natarii/MegaGRRL/firmware/main/options.c

#include "options.h"
#include "player.h"
#include "esp_log.h"
#include "driver.h"
#include "leddrv.h"
#include "loader.h"
#include "userled.h"
#include "ui/filebrowser.h"
#include "player.h"
#include "clk.h"
#include "pitch.h"
#include "ui.h"
#include <rom/crc.h>
#include "queue.h"
#include "sdcard.h"
#include "ui/modal.h"
#include "logmgr.h"

static const char* TAG = "OptionsMgr";

static volatile bool OptionsMgr_Unsaved = false;
static volatile uint8_t OptionsMgr_ShittyTimer = 0;

const char *OptionCatNames[OPTION_CATEGORY_COUNT] = {
    "General",
    "File Browser",
    "LEDs",
    "Playback",
    "Advanced",
    "Beta Features",
    //"Screen", portable only, so getting rid of it for now
};

static void opts_mutingupdate() {
    xEventGroupSetBits(Driver_CommandEvents, DRIVER_EVENT_UPDATE_MUTING);
}

static void opts_pitchupdate() {
    Pitch_Adjust(Pitch_Get()); //this will snap down to the max locked clock if they switch from unlocked -> locked
}

static void wrap_leddrv_updatebrightness() {
    LedDrv_UpdateBrightness(false);
}

static bool loaded[OPTION_COUNT];

//last used: 0018
const option_t Options[OPTION_COUNT] = {
    {
        0x0001,
        "Play mode",
        "Playlist behavior",
        OPTION_CATEGORY_PLAYBACK,
        OPTION_TYPE_NUMERIC,
        OPTION_SUBTYPE_PLAYMODE,
        &Player_RepeatMode,
        REPEAT_ALL,
        NULL,
        NULL
    },
    {
        0x0000,
        "Loop count",
        "Number of times the looping section of the track should be played",
        OPTION_CATEGORY_PLAYBACK,
        OPTION_TYPE_NUMERIC,
        OPTION_SUBTYPE_LOOPS,
        &Player_LoopCount,
        2,
        NULL,
        NULL
    },/*
    {
        "vgm_trim mitigation",
        "Silence erroneous notes at start of track caused by vgm_trim.",
        OPTION_CATEGORY_PLAYBACK,
        OPTION_TYPE_BOOL,
        &Driver_MitigateVgmTrim,
        true,
        NULL
    },*//*
    {
        "Allow PCM across block boundaries",
        "Allow PCM to be played across data block boundaries. No VGMs are known to require this, so it is recommended to leave this off. Enabling this may cause significant slowdown.",
        OPTION_CATEGORY_PLAYBACK,
        OPTION_TYPE_BOOL,
        NULL, //
        false,
        NULL
    },
    {
        "Correct DCSG frequency",
        "Automatically correct for differences between discrete TI DCSGs and Sega VDP DCSGs when channel frequency is set to 0.",
        OPTION_CATEGORY_PLAYBACK,
        OPTION_TYPE_BOOL,
        &Driver_FixDcsgFrequency,
        true,
        NULL
    },*/
    {
        0x0012,
        "Shuffle",
        "Randomize order of playback",
        OPTION_CATEGORY_PLAYBACK,
        OPTION_TYPE_BOOL,
        OPTION_SUBTYPE_SHUFFLE,
        &Queue_Shuffle,
        false,
        NULL,
        NULL
    },
    {
        0x0003,
        "Stereo/Mono toggle",
        "Setting this to mono will force mono sound in all VGMs.",
        OPTION_CATEGORY_PLAYBACK,
        OPTION_TYPE_BOOL,
        OPTION_SUBTYPE_STEREOMONO,
        &Driver_ForceMono,
        false,
        opts_mutingupdate,
        opts_mutingupdate
    },
    {
        0x0015,
        "LED brightness",
        "Overall LED brightness",
        OPTION_CATEGORY_LEDS,
        OPTION_TYPE_NUMERIC,
        OPTION_SUBTYPE_BRIGHTNESS,
        &LedDrv_Brightness,
        5,
        wrap_leddrv_updatebrightness,
        wrap_leddrv_updatebrightness
    },
    {
        0x000e,
        "Fade out at end",
        "Enables and disables fading out at the end of each track.",
        OPTION_CATEGORY_PLAYBACK,
        OPTION_TYPE_BOOL,
        OPTION_SUBTYPE_NONE,
        &Driver_FadeEnabled,
        true,
        NULL,
        NULL
    },
    {
        0x000f,
        "Fade length",
        "Length of fade out, in seconds",
        OPTION_CATEGORY_PLAYBACK,
        OPTION_TYPE_NUMERIC,
        OPTION_SUBTYPE_FADELENGTH,
        &Driver_FadeLength,
        3,
        NULL,
        NULL
    },
    {
        0x0002,
        "Ignore zero-sample loops",
        "Some badly made VGMs specify a loop offset without a loop length. Deflemask is known to do this. Turning this option off will fix looping in some broken VGMs, but will cause unwanted looping in other broken VGMs.",
        OPTION_CATEGORY_PLAYBACK,
        OPTION_TYPE_BOOL,
        OPTION_SUBTYPE_NONE,
        &Loader_IgnoreZeroSampleLoops,
        true,
        NULL,
        NULL
    },
    {
        0x0016,
        "Skip unsupported VGMs",
        "Skip VGMs that cannot be played on the hardware.",
        OPTION_CATEGORY_PLAYBACK,
        OPTION_TYPE_BOOL,
        OPTION_SUBTYPE_NONE,
        &Player_SkipUnsupported,
        true,
        NULL,
        NULL
    },
    {
        0x0017,
        "Assume SEGA DCSG",
        "Improve support for SEGA console VGM files by assuming the SN76489 is the SEGA type. This should only be disabled when playing VGMs from systems using discrete SN76489 chips.",
        OPTION_CATEGORY_PLAYBACK,
        OPTION_TYPE_BOOL,
        OPTION_SUBTYPE_NONE,
        &Driver_AssumeSegaDcsg,
        true,
        NULL,
        NULL
    },
    {
        0x0005,
        "User LED A source",
        "Sets the source of User LED A.",
        OPTION_CATEGORY_LEDS,
        OPTION_TYPE_NUMERIC,
        OPTION_SUBTYPE_USERLED,
        &UserLedMgr_Source[0],
        USERLED_SRC_PLAYPAUSE,
        NULL,
        NULL
    },
    {
        0x0006,
        "User LED B source",
        "Sets the source of User LED B.",
        OPTION_CATEGORY_LEDS,
        OPTION_TYPE_NUMERIC,
        OPTION_SUBTYPE_USERLED,
        &UserLedMgr_Source[1],
        USERLED_SRC_DISK_ALL,
        NULL,
        NULL
    },
    {
        0x0007,
        "User LED C source",
        "Sets the source of User LED C.",
        OPTION_CATEGORY_LEDS,
        OPTION_TYPE_NUMERIC,
        OPTION_SUBTYPE_USERLED,
        &UserLedMgr_Source[2],
        USERLED_SRC_NONE,
        NULL,
        NULL
    },
    {
        0x0008,
        "Sort directory contents",
        "Enabling this sorts directory contents according to the sorting options. When disabled, contents will be displayed in the order they are found in the filesystem.",
        OPTION_CATEGORY_FILEBROWSER,
        OPTION_TYPE_BOOL,
        OPTION_SUBTYPE_NONE,
        &Ui_FileBrowser_Sort,
        true,
        Ui_FileBrowser_InvalidateDirEntry,
        NULL
    },
    {
        0x0009,
        "Alphabetical sort direction",
        "Sets whether directory contents are sorted in ascending or descending order.",
        OPTION_CATEGORY_FILEBROWSER,
        OPTION_TYPE_NUMERIC,
        OPTION_SUBTYPE_SORTDIR,
        &Ui_FileBrowser_SortDir,
        SORT_ASCENDING,
        Ui_FileBrowser_InvalidateDirEntry,
        NULL
    },
    {
        0x000a,
        "Sort dirs before files",
        "Sets whether directories appear before files.",
        OPTION_CATEGORY_FILEBROWSER,
        OPTION_TYPE_BOOL,
        OPTION_SUBTYPE_NONE,
        &Ui_FileBrowser_DirsBeforeFiles,
        true,
        Ui_FileBrowser_InvalidateDirEntry,
        NULL
    },
    {
        0x0011,
        "Text scroll type",
        "Method by which long text will be scrolled",
        OPTION_CATEGORY_GENERAL,
        OPTION_TYPE_NUMERIC,
        OPTION_SUBTYPE_SCROLLTYPE,
        &Ui_ScrollType,
        SCROLLTYPE_PINGPONG,
        NULL, //note: if there are ever any global ui elements this applies to, we need to set a callback to force changes on them
        NULL
    },
    {
        0x000b,
        "Overwrite VGZ files",
        "When this is enabled, VGZ files will be overwritten with extracted VGM equivalents when first played. This will replace the files on the SD card, but will result in much shorter track load times on future plays.",
        OPTION_CATEGORY_GENERAL,
        OPTION_TYPE_BOOL,
        OPTION_SUBTYPE_NONE,
        &Player_UnvgzReplaceOriginal,
        true,
        NULL,
        NULL
    },
    {
        0x000c,
        "Narrow font",
        "Use a narrow font in the file browser.",
        OPTION_CATEGORY_FILEBROWSER,
        OPTION_TYPE_BOOL,
        OPTION_SUBTYPE_NONE,
        &Ui_FileBrowser_Narrow,
        false,
        NULL,
        NULL
    },
    {
        0x000d,
        "Unlock pitch",
        "Allow additional pitch adjustment. Warning: Sound chips will be overclocked.",
        OPTION_CATEGORY_ADVANCED,
        OPTION_TYPE_BOOL,
        OPTION_SUBTYPE_NONE,
        &Clk_Unlock,
        false,
        opts_pitchupdate,
        NULL
    },
    {
        0x0010,
        "Fast OPNA ADPCM upload",
        "Increases OPNA ADPCM upload speed. Warning: Sound chip will be overclocked.",
        OPTION_CATEGORY_ADVANCED,
        OPTION_TYPE_BOOL,
        OPTION_SUBTYPE_NONE,
        &Loader_FastOpnaUpload,
        false,
        NULL,
        NULL
    },
    {
        0x0014,
        "Log level",
        "Change the serial port log level. Values other than Normal will cause slight performance decrease.",
        OPTION_CATEGORY_ADVANCED,
        OPTION_TYPE_NUMERIC,
        OPTION_SUBTYPE_LOGLEVEL,
        &logmgr_loglevel,
        0,
        logmgr_update_loglevel,
        NULL
    },
    {
        0x0018,
        "Enable fast-forwarding",
        "Enables beta support for fast-forwarding through VGMs.",
        OPTION_CATEGORY_BETA,
        OPTION_TYPE_BOOL,
        OPTION_SUBTYPE_NONE,
        &Player_EnableFastForward,
        false,
        NULL,
        NULL
    },
};

static void file_error() {
    modal_show_simple(TAG, "SD Card Error", "There was an error saving settings to the SD card.\nPlease check that the card is inserted and has free space.", LV_SYMBOL_OK " OK");
    Sdcard_Invalidate();
    Ui_Screen = UISCREEN_MAINMENU;
}

void OptionsMgr_Save() {
    ESP_LOGW(TAG, "saving options");
    FILE *f = fopen("/sd/.mega/options.mgo", "w");
    if (!f) {
        OptionsMgr_Unsaved = true;
        file_error();
        ESP_LOGE(TAG, "IO error opening options file for write...");
        return;
    }
    uint32_t tmp = OPTIONS_VER;
    fwrite(&tmp, 1, 1, f);
    uint32_t crc = 0;
    fwrite(&crc, 4, 1, f); //alloc space for crc
    tmp = OPTION_COUNT;
    fwrite(&tmp, 1, 1, f);
    crc = crc32_le(crc, (uint8_t*)&tmp, 1);
    for (uint8_t i=0;i<OPTION_COUNT;i++) {
        fwrite(&Options[i].uid, 2, 1, f);
        crc = crc32_le(crc, (uint8_t*)&Options[i].uid, 2);
        if (Options[i].var == NULL) {
            tmp = 0;
            fwrite(&tmp, 1, 1, f);
            crc = crc32_le(crc, (uint8_t*)&tmp, 1);
            continue;
        }
        fwrite((uint8_t*)Options[i].var, 1, 1, f);
        crc = crc32_le(crc, (uint8_t*)Options[i].var, 1);
    }
    //now write out the crc
    fseek(f, 1, SEEK_SET);
    fwrite(&crc, 4, 1, f);
    if (ferror(f)) {
        OptionsMgr_Unsaved = true;
        file_error();
        ESP_LOGE(TAG, "IO error writing options file...");
        fclose(f);
        return;
    }
    fclose(f);
    ESP_LOGW(TAG, "options saved");
}

static uint8_t loadoptionsfile(const char *filename) {
    ESP_LOGI(TAG, "checking options file %s", filename);
    FILE *f = fopen(filename, "r");
    if (f == NULL) {
        ESP_LOGI(TAG, "no options file exists");
        return 1;
    }
    uint32_t tmp = 0;
    fread(&tmp, 1, 1, f);
    //note: we still support version A0 files, it was the ver prior to the CRC being added
    if (tmp != OPTIONS_VER && tmp != 0xa0) {
        ESP_LOGW(TAG, "options file bad ver 0x%02x", tmp);
        fclose(f);
        return 2;
    }
    ESP_LOGI(TAG, "file ver 0x%02x", tmp);
    if (tmp != 0xa0) { //we have a crc
        ESP_LOGI(TAG, "Verifying crc");
        fread(&tmp, 4, 1, f); //file's crc
        uint32_t curpos = ftell(f);
        fseek(f, 0, SEEK_END);
        uint32_t remaining = ftell(f) - curpos;
        //nobody else is using pcmbuf right now, so we can stash some stuff there
        fseek(f, curpos, SEEK_SET);
        fread(Driver_PcmBuf, 1, remaining, f);
        uint32_t crc = 0;
        crc = crc32_le(crc, Driver_PcmBuf, remaining);
        if (tmp != crc) {
            ESP_LOGE(TAG, "options file bad crc!!!");
            fclose(f);
            return 3;
        }
        fseek(f, curpos, SEEK_SET); //back to where we were
        ESP_LOGI(TAG, "crc all good");
        tmp = 0;
    } else {
        ESP_LOGI(TAG, "Old version, no crc to verify");
    }
    fread(&tmp, 1, 1, f);
    ESP_LOGI(TAG, "file contains %d options", tmp);
    for (uint8_t i=0;i<tmp;i++) {
        uint16_t uid = 0;
        fread(&uid, 2, 1, f);
        uint8_t v = 0;
        fread(&v, 1, 1, f);
        bool found = false;
        for (uint8_t j=0;j<OPTION_COUNT;j++) {
            if (Options[j].uid == uid) {
                found = true;
                if (uid == 0x0011 && v == 2) { //"truncate" scroll type got deleted
                    ESP_LOGW(TAG, "Fixing unsupported scroll type");
                    v = SCROLLTYPE_PINGPONG;
                    OptionsMgr_Touch();
                }
                if (Options[j].var != NULL) *(volatile uint8_t*)Options[j].var = v;
                if (Options[j].cb_initial != NULL) Options[j].cb_initial();
                loaded[j] = true;
                ESP_LOGI(TAG, "applied option uid %d - %d", uid, v);
                break;
            }
        }
        if (!found) {
            if (uid == 0x0004) { //old led brightness, new is 0015
                //find the nearest new brightness setting to the old one
                uint8_t newval = 0;
                for (uint8_t j=0;j<sizeof(global_bright_lut);j++) {
                    if (global_bright_lut[j] > v) break;
                    newval = j;
                }
                ESP_LOGW(TAG, "Remapping old LED brightness %d to new value %d (%d)", v, newval, global_bright_lut[newval]);
                for (uint8_t j=0;j<OPTION_COUNT;j++) {
                    if (Options[j].uid == 0x0015) {
                        if (Options[j].var != NULL) *(volatile uint8_t*)Options[j].var = newval;
                        if (Options[j].cb_initial != NULL) Options[j].cb_initial();
                        loaded[j] = true;
                        break;
                    }
                }
                OptionsMgr_Touch();
            } else {
                ESP_LOGW(TAG, "skipping unknown option uid %d", uid);
            }
        }
    }
    fclose(f);
    ESP_LOGI(TAG, "finished loading options file");
    return 0;
}

void OptionsMgr_Setup() {
    //load options, apply defaults if file not found, if file is corrupt try a backup
    memset(&loaded, false, OPTION_COUNT);

    uint8_t ret = loadoptionsfile("/sd/.mega/options.mgo");
    if (ret == 3) { //corrupt, try the backup
        ret = loadoptionsfile("/sd/.mega/options.bak");
        //return value doesn't really matter now, if it's bad version/corrupt/doesn't exist it just won't apply anything, and we'll set defaults below
    } else if (ret == 0) { //loaded alright, let's take a backup
        ESP_LOGI(TAG, "Backing up options file...");
        FILE *o = fopen("/sd/.mega/options.mgo", "r");
        FILE *b = fopen("/sd/.mega/options.bak", "w");
        fseek(o, 0, SEEK_END);
        uint32_t s = ftell(o);
        fseek(o, 0, SEEK_SET);
        fread(Driver_PcmBuf, 1, s, o);
        fwrite(Driver_PcmBuf, 1, s, b);
        fclose(b);
        fclose(o);
        ESP_LOGI(TAG, "Backup done");
    }

    for (uint8_t i=0;i<OPTION_COUNT;i++) {
        if (!loaded[i]) {
            if (Options[i].var != NULL) *(volatile uint8_t*)Options[i].var = (uint8_t)Options[i].defaultval;
            if (Options[i].cb_initial != NULL) Options[i].cb_initial();
            ESP_LOGW(TAG, "applied defaults for option uid %d", Options[i].uid);
        }
    }

    ESP_LOGI(TAG, "done");
}

void OptionsMgr_Touch() {
    OptionsMgr_Unsaved = true;
    OptionsMgr_ShittyTimer = 0;
}

void OptionsMgr_Main() {
    while (1) {
        if (OptionsMgr_Unsaved && OptionsMgr_ShittyTimer++ == 2) {
            OptionsMgr_ShittyTimer = 0;
            if (Sdcard_IsOnline()) {
                OptionsMgr_Unsaved = false;
                OptionsMgr_Save();
            } else {
                ESP_LOGW(TAG, "Skipping saving, SD card is offline");
            }
        }
        vTaskDelay(pdMS_TO_TICKS(1000));
    }
}
