natarii/MegaGRRL/firmware/main/img.c

#include "lvgl.h"
#include "hal.h"

#ifndef LV_ATTRIBUTE_MEM_ALIGN
#define LV_ATTRIBUTE_MEM_ALIGN
#endif

#ifdef HWVER_PORTABLE
const LV_ATTRIBUTE_MEM_ALIGN uint8_t img_frame_map[] = {
  0xff, 0xff, 0xff, 0xff, 	/*Color of index 0*/
  0x00, 0x00, 0x00, 0xff, 	/*Color of index 1*/

  0x00, 0x00, 0x00, 0x00, 0x00, 0x00, 0x00, 
  0x00, 0x00, 0x00, 0x00, 0x00, 0x00, 0x00, 
  0x3f, 0xff, 0xff, 0xff, 0xff, 0xff, 0x00, 
  0x3f, 0xff, 0xff, 0xff, 0xff, 0xff, 0x00, 
  0x3f, 0xff, 0xff, 0xff, 0xff, 0xff, 0x00, 
  0x3f, 0xff, 0xff, 0xff, 0xff, 0xff, 0x00, 
  0x3f, 0xff, 0xff, 0xff, 0xff, 0xff, 0x00, 
  0x3f, 0xff, 0xf0, 0x00, 0x00, 0x01, 0x00, 
  0x3f, 0xff, 0xf7, 0xff, 0xff, 0xfd, 0x00, 
  0x39, 0x9f, 0xf7, 0xff, 0xff, 0xfd, 0x00, 
  0x39, 0x9f, 0xf7, 0xff, 0xff, 0xfd, 0x00, 
  0x3f, 0xff, 0xf7, 0xff, 0xff, 0xfd, 0x00, 
  0x3f, 0xff, 0xf7, 0xff, 0xff, 0xfd, 0x00, 
  0x39, 0x9f, 0xf7, 0xff, 0xff, 0xfd, 0x00, 
  0x39, 0x9f, 0xf7, 0xff, 0xff, 0xfd, 0x00, 
  0x3f, 0xff, 0xf7, 0xff, 0xff, 0xfd, 0x00, 
  0x3f, 0xff, 0xf7, 0xff, 0xff, 0xfd, 0x00, 
  0x39, 0x9f, 0xf7, 0xff, 0xff, 0xfd, 0x00, 
  0x39, 0x9f, 0xf7, 0xff, 0xff, 0xfd, 0x00, 
  0x3f, 0xff, 0xf7, 0xff, 0xff, 0xfd, 0x00, 
  0x3f, 0xff, 0xf7, 0xff, 0xff, 0xfd, 0x00, 
  0x39, 0xff, 0xf7, 0xff, 0xff, 0xfd, 0x00, 
  0x39, 0xff, 0xf7, 0xff, 0xff, 0xfd, 0x00, 
  0x3f, 0xff, 0xf7, 0xff, 0xff, 0xfd, 0x00, 
  0x3f, 0xff, 0xf7, 0xff, 0xff, 0xfd, 0x00, 
  0x39, 0xff, 0xf7, 0xff, 0xff, 0xfd, 0x00, 
  0x39, 0xff, 0xf7, 0xff, 0xff, 0xfd, 0x00, 
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
};

const lv_img_dsc_t img_kunoichilabs_smol = {
  .header.always_zero = 0,
  .header.w = 157,
  .header.h = 18,
  .data_size = 1486,
  .header.cf = LV_IMG_CF_INDEXED_4BIT,
  .data = img_kunoichilabs_smol_map,
};
