natarii/MegaGRRL/firmware/main/vgm.c

#include "vgm.h"
#include "esp_log.h"
#include "math.h"

static const char* TAG = "Vgm";

static const uint8_t CommandLengthLUT[256] = {
    /*  0  1  2  3  4  5  6  7  8  9  a  b  c  d  e  f*/
        0, 0, 0, 0, 0, 0, 0, 0, 0, 0, 0, 0, 0, 0, 0, 0, //0x00
        0, 0, 0, 0, 0, 0, 0, 0, 0, 0, 0, 0, 0, 0, 0, 0, //0x10
        0, 0, 0, 0, 0, 0, 0, 0, 0, 0, 0, 0, 0, 0, 0, 0, //0x20
        2, 2, 0, 0, 0, 0, 0, 0, 0, 0, 0, 0, 0, 0, 0, 2, //0x30
        0, 0, 0, 0, 0, 0, 0, 0, 0, 0, 0, 0, 0, 0, 0, 2, //0x40
        2, 3, 3, 3, 3, 3, 3, 3, 3, 3, 3, 3, 3, 3, 3, 3, //0x50
        0, 3, 1, 1, 0, 0, 1, 0, 0, 0, 0, 0, 0, 0, 0, 0, //0x60
        1, 1, 1, 1, 1, 1, 1, 1, 1, 1, 1, 1, 1, 1, 1, 1, //0x70
        1, 1, 1, 1, 1, 1, 1, 1, 1, 1, 1, 1, 1, 1, 1, 1, //0x80
        5, 5, 6,11, 2, 5, 0, 0, 0, 0, 0, 0, 0, 0, 0, 0, //0x90
        3, 3, 3, 3, 3, 3, 3, 3, 3, 3, 3, 3, 3, 3, 3, 3, //0xa0
        3, 3, 3, 3, 3, 3, 3, 3, 3, 3, 3, 3, 3, 3, 3, 3, //0xb0
        4, 4, 4, 4, 4, 4, 4, 4, 4, 4, 4, 4, 4, 4, 4, 4, //0xc0
        4, 4, 4, 4, 4, 4, 4, 0, 0, 0, 0, 0, 0, 0, 0, 0, //0xd0
        5, 5, 0, 0, 0, 0, 0, 0, 0, 0, 0, 0, 0, 0, 0, 0, //0xe0
        0, 0, 0, 0, 0, 0, 0, 0, 0, 0, 0, 0, 0, 0, 0, 2, //0xf0
};

uint8_t VgmCommandLength(uint8_t Command) { //including the command itself. only for fixed size commands
    uint8_t val = CommandLengthLUT[Command];
    if (val) return val;
    ESP_LOGW(TAG, "Vgm_CommandLength got bad command 0x%02x !!", Command);
    return 0xff;
}

bool VgmCommandIsFixedSize(uint8_t Command) {
    if (Command == 0x67 || Command == 0x68) { //data block, pcm ram write
        return false;
    }
    return true;
}

bool VgmParseHeader(FILE *f, VgmInfoStruct_t *info) {
    fseek(f, 0, SEEK_SET);

    uint32_t magic;
    fread(&magic, 4, 1, f);
    if (magic != 0x206d6756) {
        ESP_LOGE(TAG, "Bad magic !!");
        return false;
    }

    fread(&info->EofOffset, 4, 1, f);
    uint8_t tempver[4];
    fread(&tempver, 4, 1, f);
    //decode silly bcd version no
    info->Version = 0;
    uint8_t exp = 0;
    for (uint8_t i=0;i<4;i++) {
        info->Version += (uint32_t)(tempver[i] & 0xf)*(uint32_t)pow(10,exp++);
        info->Version += (uint32_t)(tempver[i]>>4)*(uint32_t)pow(10,exp++);
    }

    fseek(f, 0, SEEK_END);
    size_t sz = ftell(f);
    fseek(f, 0x14, SEEK_SET);
    fread(&info->Gd3Offset, 4, 1, f);
    if (info->Gd3Offset > sz) info->Gd3Offset = 0; //catch wacked out gd3 offset
    if (info->Gd3Offset > 0) info->Gd3Offset += 0x14;
    fread(&info->TotalSamples, 4, 1, f);
    fread(&info->LoopOffset, 4, 1, f);
    if (info->LoopOffset > 0) info->LoopOffset += 0x1c;
    fread(&info->LoopSamples, 4, 1, f);
    if (info->Version >= 101) fread(&info->Rate, 4, 1, f);

    //NB: finding the data offset is more confusing than you may think, due to errors/omissions in the vgm spec.
    //from the spec:
    //[VGM 1.50 additions:]
    //0x34: VGM data offset (32 bits)
    //        Relative offset to VGM data stream.
    //        If the VGM data starts at absolute offset 0x40, this will contain
    //        value 0x0000000C. For versions prior to 1.50, it should be 0 and the
    //        VGM data must start at offset 0x40.
    //however, this is not the full story
    //official vgm tools (vgmplay, vgm2txt) consider a value of 0 on a >=1.50 vgm to be equivalent to an 0x40 start offset (absolute)
    //this is implemented differently depending on the software. vgm2txt silently considers a value of 0 to be equivalent to 0x0c regardless of version
    //however vgmplay considers 0 to be an error, forces the start offset to 0x40, and outputs a warning message
    //i have seen this value be 0 on 1.51 vgms "in the wild", so we must handle it even though it's not actually part of the spec.
    if (info->Version >= 150) {
        fseek(f, 0x34, SEEK_SET);
        fread(&info->DataOffset, 4, 1, f);
        if (info->DataOffset == 0) info->DataOffset = 0x0c; //handle strange maybe-not-compliant vgms
        info->DataOffset += 0x34;
    } else {
        info->DataOffset = 0x40;
    }

    if (info->Version >= 160 && info->DataOffset > 0x7c) {
        fseek(f, 0x7c, SEEK_SET);
        fread(&info->VolumeModifier, 1, 1, f);
        if (info->DataOffset > 0x7e) {
            fseek(f, 1, SEEK_CUR);
            fread(&info->LoopBase, 1, 1, f);
        }
    }

    if (info->Version >= 151 && info->DataOffset > 0x7f) {
        fseek(f, 0x7f, SEEK_SET);
        fread(&info->LoopModifier, 1, 1, f);
    }

    if (info->Version >= 170 && info->DataOffset > (0xbc+0x04)) {
        fseek(f, 0xbc, SEEK_SET);
        fread(&info->ExtraHeaderOffset, 4, 1, f);
    }

    return true;
}

bool VgmParseDevices(FILE *f, VgmInfoStruct_t *info, VgmDeviceStruct_t *devices) {
    return false;
}

bool VgmParseDataBlocks(FILE *f, VgmInfoStruct_t *info, VgmDataBlockStruct_t *blocks) {
    return false;
}

bool VgmParseDataBlock(FILE *f, VgmDataBlockStruct_t *block) {
    fseek(f,1,SEEK_CUR); //skip 0x66
    fread(&block->Type,1,1,f);
    fread(&block->Size,4,1,f);
    uint8_t seekoff = 0;
    if (block->Type <= 0x3f) { //uncompressed data
        //nothing fancy to do here...
        seekoff = 0;
        ESP_LOGI(TAG, "Parsed uncompressed datablock: type %02x, size %d", block->Type, block->Size);
    } else if (block->Type <= 0x7e) { //compressed data
        fread(&block->CompressionType,1,1,f);
        fread(&block->UncompressedSize,4,1,f);
        fread(&block->BitsDecompressed,1,1,f);
        fread(&block->BitsCompressed,1,1,f);
        fread(&block->Subtype,1,1,f);
        fread(&block->CompValue,2,1,f);
        if (block->CompressionType == 0x01 && block->Subtype != 0) {
            ESP_LOGE(TAG, "Error parsing datablock: DPCM subtype != 0");
            return false;
        }
        seekoff = 10;
        ESP_LOGI(TAG, "Parsed compressed datablock: type %02x, size %d, compression type %02x, uncompressed size %d, bitsD %d, bitsC %d, subtype %02x, CompValue %d", block->Type, block->Size, block->CompressionType, block->UncompressedSize, block->BitsDecompressed, block->BitsCompressed, block->Subtype, block->CompValue);
    } else if (block->Type == 0x7f) {
        fread(&block->CompressionType,1,1,f);
        fread(&block->Subtype,1,1,f);
        fread(&block->BitsDecompressed,1,1,f);
        fread(&block->BitsCompressed,1,1,f);
        fread(&block->CompValue,2,1,f);
        seekoff = 6;
        ESP_LOGI(TAG, "Parsed datablock decompression table: size %d, comp type %02x, subtype %02x, bitsD %d, bitsC %d, CompValue %d", block->Size, block->CompressionType, block->Subtype, block->BitsDecompressed, block->BitsCompressed, block->CompValue);
    } else if (block->Type == 0x81) {
        fread(&block->RomSize,4,1,f);
        fread(&block->StartAddress,4,1,f);
        seekoff = 8;
        ESP_LOGI(TAG, "Parsed OPNA ADPCM datablock: rom size %d, offset %d, adpcm data size %d", block->RomSize, block->StartAddress, block->Size-8);
    } else if (block->Type == 0xc1) {
        fread(&block->StartAddress,4,1,f);
        seekoff = 4;
        ESP_LOGI(TAG, "Parsed RF5C164 datablock: offset %d, size %d", block->StartAddress, block->Size-4);
    } else {
        seekoff = 0;
        ESP_LOGW(TAG, "Found unsupported datablock");
    }
    block->Offset = ftell(f);
    if (feof(f)) {
        ESP_LOGE(TAG, "Eof parsing datablock !!");
        return false;
    }
    fseek(f,block->Size - seekoff,SEEK_CUR); //skip to end of block
    return true;
}
