natarii/MegaGRRL/firmware/main/lcddma.h

#ifndef AGR_LCDDMA_H
#define AGR_LCDDMA_H

#include "freertos/FreeRTOS.h"
#include "esp_system.h"
#include "freertos/semphr.h"

//todo make this not a giant mess

// ==== Display commands constants ====
#define TFT_INVOFF     0x20
#define TFT_INVON      0x21
#define TFT_DISPOFF    0x28
#define TFT_DISPON     0x29
#define TFT_MADCTL	   0x36
#define TFT_PTLAR 	   0x30
#define TFT_ENTRYM 	   0xB7

#define TFT_CMD_NOP			0x00
#define TFT_CMD_SWRESET		0x01
#define TFT_CMD_RDDID		0x04
#define TFT_CMD_RDDST		0x09

#define TFT_CMD_SLPIN		0x10
#define TFT_CMD_SLPOUT		0x11
#define TFT_CMD_PTLON		0x12
#define TFT_CMD_NORON		0x13

#define TFT_CMD_RDMODE		0x0A
#define TFT_CMD_RDMADCTL	0x0B
#define TFT_CMD_RDPIXFMT	0x0C
#define TFT_CMD_RDIMGFMT	0x0D
#define TFT_CMD_RDSELFDIAG  0x0F

#define TFT_CMD_GAMMASET	0x26

#define TFT_CMD_FRMCTR1		0xB1
#define TFT_CMD_FRMCTR2		0xB2
#define TFT_CMD_FRMCTR3		0xB3
#define TFT_CMD_INVCTR		0xB4
#define TFT_CMD_DFUNCTR		0xB6

#define TFT_CMD_PWCTR1		0xC0
#define TFT_CMD_PWCTR2		0xC1
#define TFT_CMD_PWCTR3		0xC2
#define TFT_CMD_PWCTR4		0xC3
#define TFT_CMD_PWCTR5		0xC4
#define TFT_CMD_VMCTR1		0xC5
#define TFT_CMD_VMCTR2		0xC7

#define TFT_CMD_RDID1		0xDA
#define TFT_CMD_RDID2		0xDB
#define TFT_CMD_RDID3		0xDC
#define TFT_CMD_RDID4		0xDD

#define TFT_CMD_GMCTRP1		0xE0
#define TFT_CMD_GMCTRN1		0xE1

#define TFT_CMD_POWERA		0xCB
#define TFT_CMD_POWERB		0xCF
#define TFT_CMD_POWER_SEQ	0xED
#define TFT_CMD_DTCA		0xE8
#define TFT_CMD_DTCB		0xEA
#define TFT_CMD_PRC			0xF7
#define TFT_CMD_3GAMMA_EN	0xF2

#define TFT_RGB_BGR 0x08

#define MADCTL_MY  0x80
#define MADCTL_MX  0x40
#define MADCTL_MV  0x20
#define MADCTL_ML  0x10
#define MADCTL_MH  0x04

#define TFT_CASET		0x2A
#define TFT_PASET		0x2B
#define TFT_RAMWR		0x2C
#define TFT_RAMRD		0x2E


#define TFT_CMD_PIXFMT	0x3A
#define TFT_CMD_DELAY	0xFF

extern volatile bool LcdDma_AltMode;
extern volatile bool LcdDma_Screenshot;

bool LcdDma_Setup();
void LcdDma_Main();
bool LcdDma_Mutex_Take(TickType_t Ticks);
bool LcdDma_Mutex_Give();

#endif
