natarii/MegaGRRL/firmware/main/mallocs.h

#ifndef AGR_MALLOCS_H
#define AGR_MALLOCS_H

#define DRIVER_QUEUE_SIZE 40000 //also used for old-style 2612 pcm. must be less than DACSTREAM_BUF_SIZE*DACSTREAM_PRE_COUNT!!
#define DACSTREAM_BUF_SIZE 5000
#define DACSTREAM_PRE_COUNT 16
#define MAX_OPEN_FILES 24
#define IOEXP_PORTA_QUEUE_SIZE 8
#define MAX_REALTIME_DATABLOCKS 40
#define FREAD_LOCAL_BUF 512
#define PLAYER_GD3_FIELD_SIZES 128
#define UI_KEYQUEUE_SIZE 4
#define PCM_SBUF_COUNT 6
#define PCM_SBUF_SIZE (((DACSTREAM_PRE_COUNT*DACSTREAM_BUF_SIZE)-DRIVER_QUEUE_SIZE)/PCM_SBUF_COUNT)
#define FILEBROWSER_CACHE_SIZE 33000
#define FILEBROWSER_CACHE_MAXENTRIES 2000

#endif
