natarii/MegaGRRL/firmware/main/sdcard.h

#ifndef AGR_SDCARD_H
#define AGR_SDCARD_H

#include "esp_vfs.h"
#include "esp_vfs_fat.h"
#include "vfs_fat_internal.h"
#include "driver/sdmmc_host.h"
#include "sdmmc_cmd.h"
#include "sdmmc_cmd.h"
#include "diskio.h"

uint8_t Sdcard_Setup();
void Sdcard_Destroy();
bool Sdcard_IsOnline();
void Sdcard_Invalidate();

#endif
