natarii/MegaGRRL/firmware/main/leddrv.h

#ifndef AGR_LEDDRV_H
#define AGR_LEDDRV_H
#include "freertos/FreeRTOS.h"
#include "freertos/queue.h"
#include "esp_system.h"

extern volatile uint8_t LedDrv_States[16];
extern volatile uint8_t LedDrv_Brightness;
extern volatile uint8_t LedDrv_States_ULatch[3];
extern const uint8_t global_bright_lut[17];

bool LedDrv_Setup();
bool LedDrv_Update();
void LedDrv_UpdateBrightness(bool force_off);

#endif
