natarii/MegaGRRL/firmware/main/ui/nowplaying.c

#include "freertos/FreeRTOS.h"
#include "statusbar.h"
#include "esp_log.h"
#include "lvgl.h"
#include "../lcddma.h"
#include "../ui.h"
#include "../key.h"
#include "../player.h"
#include "../taskmgr.h"
#include "../driver.h"
#include "../queue.h"
#include "../options.h"
#include "../loader.h"
#include "../pitch.h"

#include "softbar.h"

static const char* TAG = "Ui_NowPlaying";



volatile bool Ui_NowPlaying_DataAvail = false;
volatile bool Ui_NowPlaying_DriverRunning = false;

static uint8_t lastbarx = 0xff;
static EventBits_t laststatus = 0;
static UiScreen_t lastscreen = UISCREEN_FILEBROWSER;

static IRAM_ATTR lv_obj_t *container;
static lv_style_t labelstyle;
static lv_style_t textstyle;
static lv_style_t labelstyle_sm;
static lv_style_t textstyle_sm;
static IRAM_ATTR lv_obj_t *label_title;
static IRAM_ATTR lv_obj_t *label_author;
static IRAM_ATTR lv_obj_t *label_game;
static IRAM_ATTR lv_obj_t *label_time;
static IRAM_ATTR lv_obj_t *label_loop;
static IRAM_ATTR lv_obj_t *label_playlist;
static IRAM_ATTR lv_obj_t *text_title;
static IRAM_ATTR lv_obj_t *text_author;
static IRAM_ATTR lv_obj_t *text_game;
static IRAM_ATTR lv_obj_t *text_time;
static IRAM_ATTR lv_obj_t *text_loop;
static IRAM_ATTR lv_obj_t *text_playlist;
static IRAM_ATTR lv_obj_t *bar_track;
static IRAM_ATTR lv_obj_t *bar_trackloop;
static IRAM_ATTR lv_obj_t *bar_scrub;
static lv_style_t style_bar_track;
static lv_style_t style_bar_trackloop;
static lv_style_t style_bar_scrub;
static IRAM_ATTR lv_obj_t *bar_div;
static lv_style_t divstyle;
static IRAM_ATTR lv_obj_t *dpad[4];
static lv_style_t style_dpad;
static IRAM_ATTR lv_obj_t *dpadtext[4];
//this is really a mess and should be redone, but for now...
static IRAM_ATTR lv_obj_t *text_opt_shuffle;
static IRAM_ATTR lv_obj_t *text_opt_loops;
static IRAM_ATTR lv_obj_t *text_opt_pitch;
static IRAM_ATTR lv_obj_t *label_options;
static IRAM_ATTR lv_obj_t *text_opt_playmode;
static IRAM_ATTR lv_obj_t *text_opt_more;
static IRAM_ATTR lv_obj_t *text_opt_muting;
static IRAM_ATTR lv_obj_t *broken_vgm_time_warning;
static uint8_t selectedopt = 0;
static bool optionsopen = false;
static lv_style_t textstyle_sm_sel;
static char loopcountbuf[4] = {0};
static char pitchbuf[10] = "";
static const char *loading = "Nothing playing...";
static const char *broken_vgm_time_warning_text = " Playback time unavailable  due to broken VGM file";
static IRAM_ATTR uint32_t lastelapsedsecs = 0xffffffff;
static IRAM_ATTR uint32_t lastelapsedmins = 0xffffffff;
static lv_style_t style_preloadbg;
static IRAM_ATTR lv_obj_t *preload;
static IRAM_ATTR lv_obj_t *preloadbg;
static bool lastloading = false;

static char loopbuf[11]; //size?

static uint32_t map(uint32_t x, uint32_t in_min, uint32_t in_max, uint32_t out_min, uint32_t out_max) {
  return (x - in_min) * (out_max - out_min) / (in_max - in_min) + out_min;
}

static void newtrack();
static void do_tick();

void Ui_NowPlaying_Destroy() {
    LcdDma_Mutex_Take(pdMS_TO_TICKS(1000));
    lv_obj_del(container);
    LcdDma_Mutex_Give();
}

bool Ui_NowPlaying_Setup(lv_obj_t *uiscreen) {
    if (Ui_Screen_Last != UISCREEN_NOWPLAYING) lastscreen = Ui_Screen_Last;

    LcdDma_Mutex_Take(pdMS_TO_TICKS(1000));

    container = lv_cont_create(uiscreen, NULL);

    lv_style_copy(&labelstyle, &lv_style_plain);
    labelstyle.text.color = LV_COLOR_MAKE(100, 100, 230); //127,127,127);
    labelstyle.text.font = &lv_font_dejavu_18;

    lv_style_copy(&textstyle, &labelstyle);
    textstyle.text.color = LV_COLOR_MAKE(220, 220, 220); //255,255,255);

    lv_style_copy(&labelstyle_sm, &labelstyle);
    labelstyle_sm.text.font = &lv_font_dejavu_14_2bpp;
    labelstyle_sm.text.line_space = -2;

    lv_style_copy(&textstyle_sm, &textstyle);
    textstyle_sm.text.font = &lv_font_dejavu_14_2bpp;

    lv_cont_set_style(container, LV_CONT_STYLE_MAIN, &lv_style_transp);
    lv_obj_set_height(container, 250);
    lv_obj_set_width(container, 240);
    lv_obj_set_pos(container, 0, 34+1);
    //lv_cont_set_fit(container, false, false);

    label_title = lv_label_create(container, NULL);
    lv_label_set_style(label_title, LV_LABEL_STYLE_MAIN, &labelstyle);
    lv_obj_set_pos(label_title, 5, 5);
    lv_label_set_static_text(label_title, "Title");

    label_author = lv_label_create(container, NULL);
    lv_label_set_style(label_author, LV_LABEL_STYLE_MAIN, &labelstyle);
    lv_obj_set_pos(label_author, 5, 45);
    lv_label_set_static_text(label_author, "Authors");

    label_game = lv_label_create(container, NULL);
    lv_label_set_style(label_game, LV_LABEL_STYLE_MAIN, &labelstyle);
    lv_obj_set_pos(label_game, 5, 85);
    lv_label_set_static_text(label_game, "Game");

    text_title = lv_label_create(container, NULL);
    lv_label_set_style(text_title, LV_LABEL_STYLE_MAIN, &textstyle);
    lv_obj_set_pos(text_title, 5, 25);
    lv_label_set_anim_speed(text_title, 50);
    lv_label_set_static_text(text_title, loading);

    text_author = lv_label_create(container, NULL);
    lv_label_set_style(text_author, LV_LABEL_STYLE_MAIN, &textstyle);
    lv_obj_set_pos(text_author, 5, 65);
    lv_label_set_anim_speed(text_author, 50);
    lv_label_set_static_text(text_author, loading);

    text_game = lv_label_create(container, NULL);
    lv_label_set_style(text_game, LV_LABEL_STYLE_MAIN, &textstyle);
    lv_obj_set_pos(text_game, 5, 105);
    lv_label_set_anim_speed(text_game, 50);
    lv_label_set_static_text(text_game, loading);



    label_playlist = lv_label_create(container, NULL);
    lv_label_set_style(label_playlist, LV_LABEL_STYLE_MAIN, &labelstyle_sm);
    lv_obj_set_pos(label_playlist, 125, 145);
    lv_label_set_static_text(label_playlist, "Track No.");

    text_playlist = lv_label_create(container, NULL);
    lv_label_set_style(text_playlist, LV_LABEL_STYLE_MAIN, &textstyle_sm);
    lv_obj_set_pos(text_playlist, 125, 160);
    lv_label_set_static_text(text_playlist, "0 / 0");

    label_time = lv_label_create(container, NULL);
    lv_label_set_style(label_time, LV_LABEL_STYLE_MAIN, &labelstyle_sm);
    lv_obj_set_pos(label_time, 125, 175);
    lv_label_set_static_text(label_time, "Time");

    text_time = lv_label_create(container, NULL);
    lv_label_set_style(text_time, LV_LABEL_STYLE_MAIN, &textstyle_sm);
    lv_obj_set_pos(text_time, 125, 190);
    lv_label_set_static_text(text_time, "00:00 / 00:00");

    label_loop = lv_label_create(container, NULL);
    lv_label_set_style(label_loop, LV_LABEL_STYLE_MAIN, &labelstyle_sm);
    lv_obj_set_pos(label_loop, 125, 205);
    lv_label_set_static_text(label_loop, "Loop");

    text_loop = lv_label_create(container, NULL);
    lv_label_set_style(text_loop, LV_LABEL_STYLE_MAIN, &textstyle_sm);
    lv_obj_set_pos(text_loop, 125, 220); 
    strcpy(loopbuf, "1 / 1");
    lv_label_set_static_text(text_loop, loopbuf);





    lv_style_copy(&style_bar_track, &lv_style_plain);
    style_bar_track.body.main_color = LV_COLOR_MAKE(0,0,32);
    style_bar_track.body.grad_color = LV_COLOR_MAKE(0,0,200);
    lv_style_copy(&style_bar_trackloop, &lv_style_plain);
    style_bar_trackloop.body.main_color = LV_COLOR_MAKE(0,32,0);
    style_bar_trackloop.body.grad_color = LV_COLOR_MAKE(0,200,0);
    lv_style_copy(&style_bar_scrub, &lv_style_plain);
    style_bar_scrub.body.main_color = LV_COLOR_MAKE(255,255,255);
    style_bar_scrub.body.grad_color = LV_COLOR_MAKE(255,255,255);
    bar_track = lv_obj_create(container, NULL);
    lv_obj_set_style(bar_track, &style_bar_track);
    lv_obj_set_pos(bar_track, 10, 128);
    lv_obj_set_size(bar_track, 220, 10);
    bar_trackloop = lv_obj_create(container, NULL);
    lv_obj_set_style(bar_trackloop, &style_bar_trackloop);
    lv_obj_set_pos(bar_trackloop, 230, 128);
    lv_obj_set_size(bar_trackloop, 0, 10);
    bar_scrub = lv_obj_create(container, NULL);
    lv_obj_set_style(bar_scrub, &style_bar_scrub);
    lv_obj_set_pos(bar_scrub, 10, 128);
    lv_obj_set_size(bar_scrub, 2, 10);

    static lv_style_t style_time_warning;
    lv_style_copy(&style_time_warning, &lv_style_plain);
    //style_time_warning.text.font = &lv_font_monospace_8;
    style_time_warning.text.color = LV_COLOR_MAKE(255,255,255);
    broken_vgm_time_warning = lv_label_create(container, NULL);
    lv_label_set_style(broken_vgm_time_warning, LV_LABEL_STYLE_MAIN, &style_time_warning);
    lv_obj_set_pos(broken_vgm_time_warning, 13, 129);
    lv_label_set_long_mode(broken_vgm_time_warning, Ui_GetScrollType());
    lv_obj_set_width(broken_vgm_time_warning, 217);
    lv_obj_set_hidden(broken_vgm_time_warning, true);



    lv_style_copy(&divstyle, &lv_style_plain);
    divstyle.body.main_color = divstyle.body.grad_color = LV_COLOR_MAKE(255,255,255);
    bar_div = lv_obj_create(container, NULL);
    lv_obj_set_style(bar_div, &divstyle);
    lv_obj_set_pos(bar_div, 120, 128+10);
    lv_obj_set_size(bar_div, 1, 250-(128+10));

    //options
    lv_style_copy(&textstyle_sm_sel, &textstyle_sm);
    textstyle_sm_sel.text.color = LV_COLOR_MAKE(255,255,0);

    label_options = lv_label_create(container, NULL);
    lv_label_set_style(label_options, LV_LABEL_STYLE_MAIN, &labelstyle_sm);
    lv_obj_set_pos(label_options, 3, 139);
    lv_obj_set_size(label_options, 120, 100);
    lv_label_set_align(label_options, LV_LABEL_ALIGN_RIGHT);
    lv_label_set_static_text(label_options, "Play Mode\nLoop Count\nShuffle\nPitch\n\nChannel Muting\nMore Settings");

    int16_t yd = 15;
    int16_t y = 139;

    text_opt_playmode = lv_label_create(container, NULL);
    lv_label_set_style(text_opt_playmode, LV_LABEL_STYLE_MAIN, &textstyle_sm);
    lv_obj_set_pos(text_opt_playmode, 125, y);
    y += yd;
    lv_label_set_static_text(text_opt_playmode, "Repeat All");

    text_opt_loops = lv_label_create(container, NULL);
    lv_label_set_style(text_opt_loops, LV_LABEL_STYLE_MAIN, &textstyle_sm_sel);
    lv_obj_set_pos(text_opt_loops, 125, y);
    y += yd;
    lv_label_set_static_text(text_opt_loops, "2");

    text_opt_shuffle = lv_label_create(container, NULL);
    lv_label_set_style(text_opt_shuffle, LV_LABEL_STYLE_MAIN, &textstyle_sm_sel);
    lv_obj_set_pos(text_opt_shuffle, 125, y);
    y += yd;
    lv_label_set_static_text(text_opt_shuffle, "Off");

    text_opt_pitch = lv_label_create(container, NULL);
    lv_label_set_style(text_opt_pitch, LV_LABEL_STYLE_MAIN, &textstyle_sm_sel);
    lv_obj_set_pos(text_opt_pitch, 125, y);
    y += yd;
    lv_label_set_static_text(text_opt_pitch, "0%");

    y += (yd*1); //no of blank lines

    text_opt_muting = lv_label_create(container, NULL);
    lv_label_set_style(text_opt_muting, LV_LABEL_STYLE_MAIN, &textstyle_sm_sel);
    lv_obj_set_pos(text_opt_muting, 125, y);
    y += yd;
    lv_label_set_static_text(text_opt_muting, "Press C "LV_SYMBOL_RIGHT);

    text_opt_more = lv_label_create(container, NULL);
    lv_label_set_style(text_opt_more, LV_LABEL_STYLE_MAIN, &textstyle_sm_sel);
    lv_obj_set_pos(text_opt_more, 125, y);
    lv_label_set_static_text(text_opt_more, "Press C "LV_SYMBOL_RIGHT);

    lv_obj_set_hidden(label_options, true);
    lv_obj_set_hidden(text_opt_playmode, true);
    lv_obj_set_hidden(text_opt_loops, true);
    lv_obj_set_hidden(text_opt_shuffle, true);
    lv_obj_set_hidden(text_opt_pitch, true);
    lv_obj_set_hidden(text_opt_more, true);
    lv_obj_set_hidden(text_opt_muting, true);

    optionsopen = false;






    lv_style_copy(&style_dpad, &lv_style_plain);
    style_dpad.body.main_color = LV_COLOR_MAKE(127,127,127);
    style_dpad.body.grad_color = LV_COLOR_MAKE(127,127,127);
    style_dpad.body.radius = LV_RADIUS_CIRCLE;
    style_dpad.text.color = LV_COLOR_MAKE(0,0,0);
    style_dpad.text.font = &lv_font_dejavu_18;
    for (uint8_t i=0;i<4;i++) {
        dpad[i] = lv_obj_create(container, NULL);
        lv_obj_set_style(dpad[i], &style_dpad);
        lv_obj_set_size(dpad[i], 30, 30);
        dpadtext[i] = lv_label_create(dpad[i], NULL);
        lv_obj_set_style(dpadtext[i], &style_dpad);
        lv_obj_set_size(dpadtext[i], 30, 30);
    }
    lv_obj_set_pos(dpad[0], 45, 138+4);
    lv_obj_set_pos(dpad[1], 45, 250-4-30);
    lv_obj_set_pos(dpad[2], 8, 179);
    lv_obj_set_pos(dpad[3], 120-8-30, 179);
    lv_label_set_static_text(dpadtext[0], LV_SYMBOL_PLAY);
    lv_obj_set_pos(dpadtext[0], 9, 5);
    lv_label_set_static_text(dpadtext[1], LV_SYMBOL_STOP);
    lv_obj_set_pos(dpadtext[1], 7, 5);
    lv_label_set_static_text(dpadtext[2], LV_SYMBOL_LEFT);
    lv_obj_set_pos(dpadtext[2], 7, 5);
    lv_label_set_static_text(dpadtext[3], LV_SYMBOL_RIGHT);
    lv_obj_set_pos(dpadtext[3], 11, 5);
    
    lv_style_copy(&style_preloadbg, &lv_style_plain);
    style_preloadbg.body.main_color = LV_COLOR_MAKE(0,0,0);
    style_preloadbg.body.grad_color = LV_COLOR_MAKE(0,0,0);
    style_preloadbg.body.radius = LV_RADIUS_CIRCLE;
    preloadbg = lv_obj_create(container, NULL);
    lv_obj_set_style(preloadbg, &style_preloadbg);
    lv_obj_set_size(preloadbg, 56, 56);
    lv_obj_set_pos(preloadbg, 92, 97);

    preload = lv_preload_create(container, NULL);
    lv_obj_set_pos(preload, 95, 100);
    lv_obj_set_size(preload, 50, 50);


    lv_obj_set_hidden(preload, true);
    lv_obj_set_hidden(preloadbg, true);

    Ui_SoftBar_Update(2, true, "Settings", false);
    Ui_SoftBar_Update(1, true, "Browser", false);
    Ui_SoftBar_Update(0, true, LV_SYMBOL_HOME "Home", false);

    xEventGroupClearBits(Player_Status, PLAYER_STATUS_RAN_OUT);

    lastbarx = 0xff;
    laststatus = 0;
    lastelapsedsecs = 0xffffffff;
    lastelapsedsecs = 0xffffffff;
    if (Ui_NowPlaying_DriverRunning) {
        newtrack();
        do_tick();
        Ui_NowPlaying_DataAvail = false;
    }

    LcdDma_Mutex_Give();

    return true;
}

static char npnone[] = "(none)";
static IRAM_ATTR uint32_t nptimer = 0;
static char timebuf[16];
static char plsbuf[14]; //size?
static uint8_t loopcount;
static IRAM_ATTR uint32_t loopsamples;
static IRAM_ATTR uint32_t totalsamples;
static IRAM_ATTR uint32_t looppoint;
static IRAM_ATTR uint32_t totalwithloops;
static IRAM_ATTR uint32_t totalmins;
static IRAM_ATTR uint32_t totalsecs;
static IRAM_ATTR uint32_t elapsedmins;
static IRAM_ATTR uint32_t elapsedsecs;

static void calc_length() {
    totalwithloops = (looppoint + (loopsamples * Player_LoopCount)) / 44100;
    if (Driver_FadeEnabled && loopsamples) totalwithloops += Driver_FadeLength;
    totalmins = totalwithloops/60;
    totalsecs = totalwithloops%60;
    loopcount = (Player_Info.LoopOffset && loopsamples)?Player_LoopCount:1;
}

static void newtrack() { //gd3, pls position, loop count/samples
    //title
    if (strlen(Player_Gd3_Title) == 0) { //no title in gd3
        uint16_t nameoff = 0;
        for (uint16_t i=0;i<strlen(QueuePlayingFilename);i++) {
            if (QueuePlayingFilename[i] == '/') {
                nameoff = i+1;
            }
        }
        lv_label_set_text(text_title, &QueuePlayingFilename[nameoff]); //not using this as static, because we get a flash of the next track name when seeking from non-gd3 to with-gd3
    } else {
        lv_label_set_static_text(text_title, Player_Gd3_Title);
    }
    lv_label_set_long_mode(text_title, Ui_GetScrollType());
    lv_obj_set_width(text_title, 230);

    //author
    if (strlen(Player_Gd3_Author)) {
        lv_label_set_style(text_author, LV_LABEL_STYLE_MAIN, &textstyle);
        lv_label_set_static_text(text_author, &Player_Gd3_Author[0]);
    } else {
        lv_label_set_style(text_author, LV_LABEL_STYLE_MAIN, &labelstyle);
        lv_label_set_static_text(text_author, npnone);
    }
    lv_label_set_long_mode(text_author, Ui_GetScrollType());
    lv_obj_set_width(text_author, 230);

    //game
    if (strlen(Player_Gd3_Game)) {
        lv_label_set_style(text_game, LV_LABEL_STYLE_MAIN, &textstyle);
        lv_label_set_static_text(text_game, &Player_Gd3_Game[0]);
    } else {
        lv_label_set_style(text_game, LV_LABEL_STYLE_MAIN, &labelstyle);
        lv_label_set_static_text(text_game, npnone);
    }
    lv_label_set_long_mode(text_game, Ui_GetScrollType());
    lv_obj_set_width(text_game, 230);

    //playlist position
    sprintf(plsbuf, "%d / %d", QueuePosition+1, QueueLength);
    lv_label_set_static_text(text_playlist, plsbuf);

    //loop stuff
    totalsamples = Player_Info.TotalSamples;
    ESP_LOGI(TAG, "total samples %d", totalsamples);
    if (!Loader_IgnoreZeroSampleLoops && Player_Info.LoopSamples == 0 && Player_Info.LoopOffset) {
        ESP_LOGW(TAG, "broken looping vgm without IgnoreZeroSampleLoops");
        looppoint = 0;
        loopsamples = totalsamples;
    } else {
        ESP_LOGI(TAG, "vgm doesn't have broken loop");
        loopsamples = Player_Info.LoopSamples;
        looppoint = totalsamples - loopsamples;
    }
    ESP_LOGI(TAG, "loop point at %d, loop length %d samples", looppoint, loopsamples);

    //reset stuff
    lv_obj_set_pos(bar_scrub, 10, 128);

    if (Ui_NowPlaying_DriverRunning) {
        elapsedmins = Driver_Sample/44100/60;
        elapsedsecs = (Driver_Sample/44100)%60;
    } else {
        elapsedmins = elapsedsecs = 0;
    }
    if (Player_Info.LoopOffset && loopsamples && Player_LoopCount == 255) {
        sprintf(timebuf, "%02d:%02d / inf.", elapsedmins, elapsedsecs);
    } else {
        calc_length();
        sprintf(timebuf, "%02d:%02d / %02d:%02d", elapsedmins, elapsedsecs, totalmins, totalsecs);
    }
    lv_label_set_static_text(text_time, timebuf);

    //scrub
    if (totalsamples) {
        uint32_t tracklength = map(looppoint/100, 0, totalsamples/100, 0, 220);
        uint32_t looplength = map(loopsamples/100, 0, totalsamples/100, 0, 220);
        if (loopsamples && looplength == 0) looplength = 1; //make sure very short loops are still visible
        lv_obj_set_size(bar_track, tracklength, 10);
        lv_obj_set_size(bar_trackloop, looplength, 10);
        lv_obj_set_pos(bar_trackloop, 10+tracklength, 128);
    } else {
        lv_obj_set_size(bar_track, 220, 10);
        lv_obj_set_size(bar_trackloop, 0, 10);
        lv_label_set_static_text(broken_vgm_time_warning, broken_vgm_time_warning_text); //do this now, rather than once at init, to reset scroll
    }
    lv_obj_set_hidden(broken_vgm_time_warning, totalsamples>0);

    //initial dpad status - especially important if going mainmenu->nowplaying
    if (xEventGroupGetBits(Player_Status) & (PLAYER_STATUS_PAUSED|PLAYER_STATUS_NOT_RUNNING)) {
        lv_label_set_static_text(dpadtext[0], LV_SYMBOL_PLAY);
        lv_obj_set_pos(dpadtext[0], 9, 5);
    } else {
        lv_label_set_static_text(dpadtext[0], LV_SYMBOL_PAUSE);
        lv_obj_set_pos(dpadtext[0], 7, 5);
    }

    //loop
    if (Player_Info.LoopOffset && loopsamples) {
        if (Player_LoopCount < 255) {
            sprintf(loopbuf, "1 / %d", loopcount);
        } else {
            strcpy(loopbuf, "1 / inf.");
        }
    } else {
        strcpy(loopbuf, "1 / 1");
    }
    lv_label_set_static_text(text_loop, loopbuf);
}
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
